MGCorbin/biologically-inspired-perching-drone/images/image(3).png

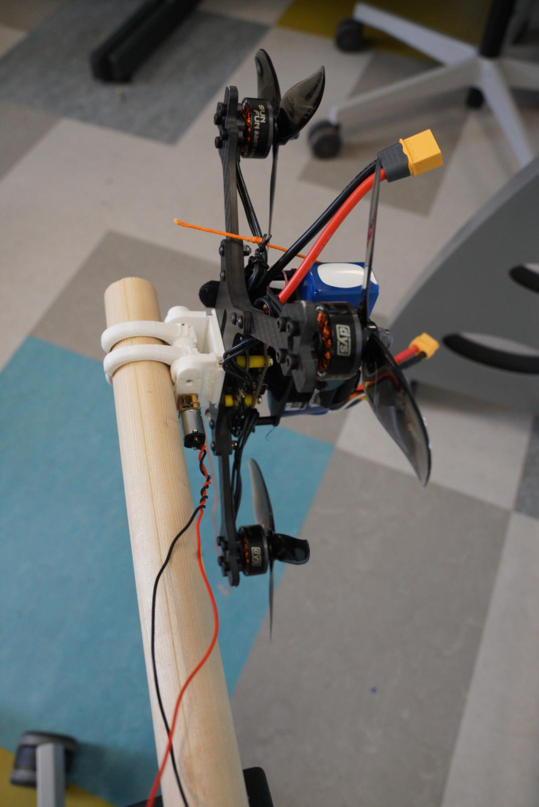
images/image(3).png
