MGCorbin/biologically-inspired-perching-drone/images/image(4).png

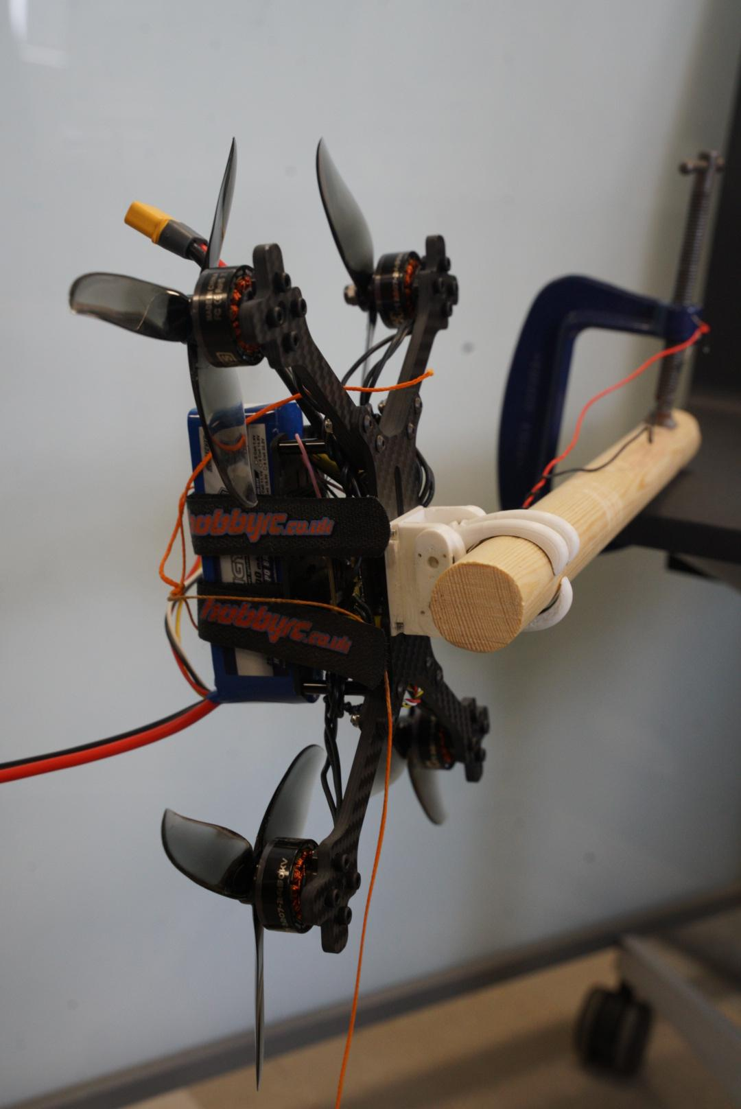
images/image(4).png
