MGCorbin/biologically-inspired-perching-drone/images/image(5).png

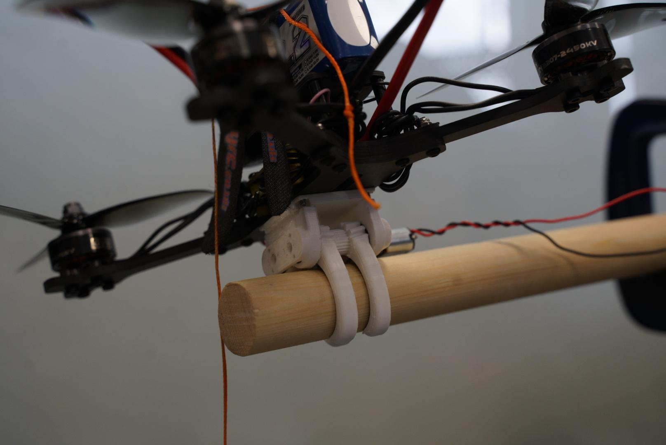
images/image(5).png
