MGCorbin/biologically-inspired-perching-drone/images/image(7).png

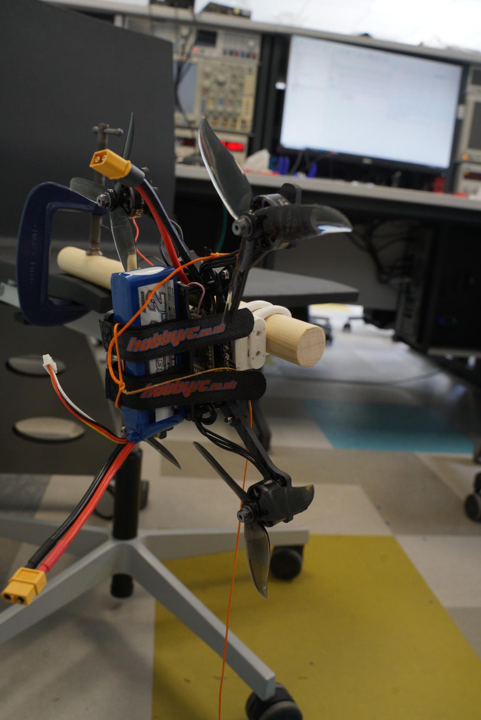
images/image(7).png
