MGCorbin/biologically-inspired-perching-drone/images/image(8).png

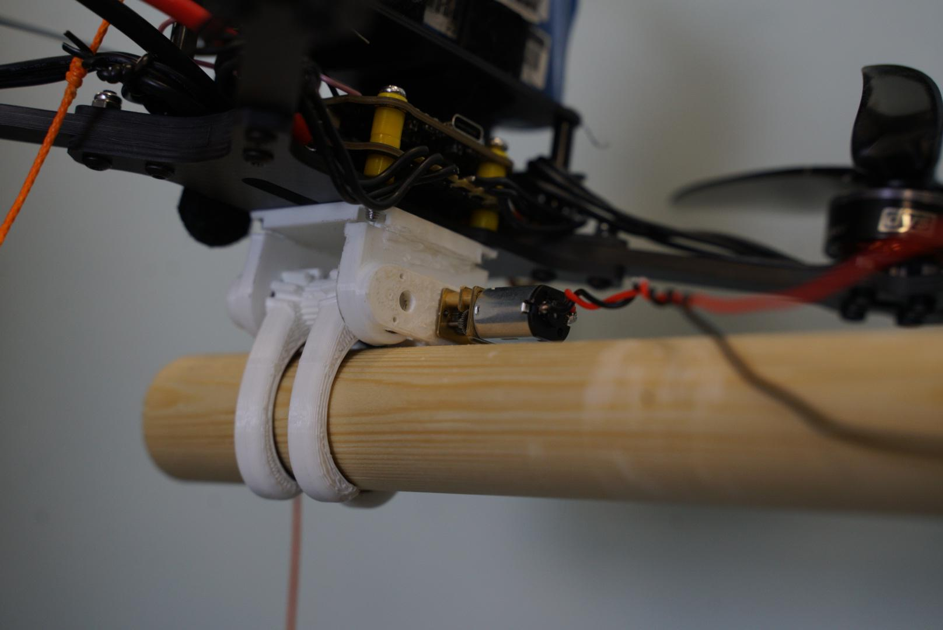
images/image(8).png
