MGCorbin/biologically-inspired-perching-drone/images/image(9).png

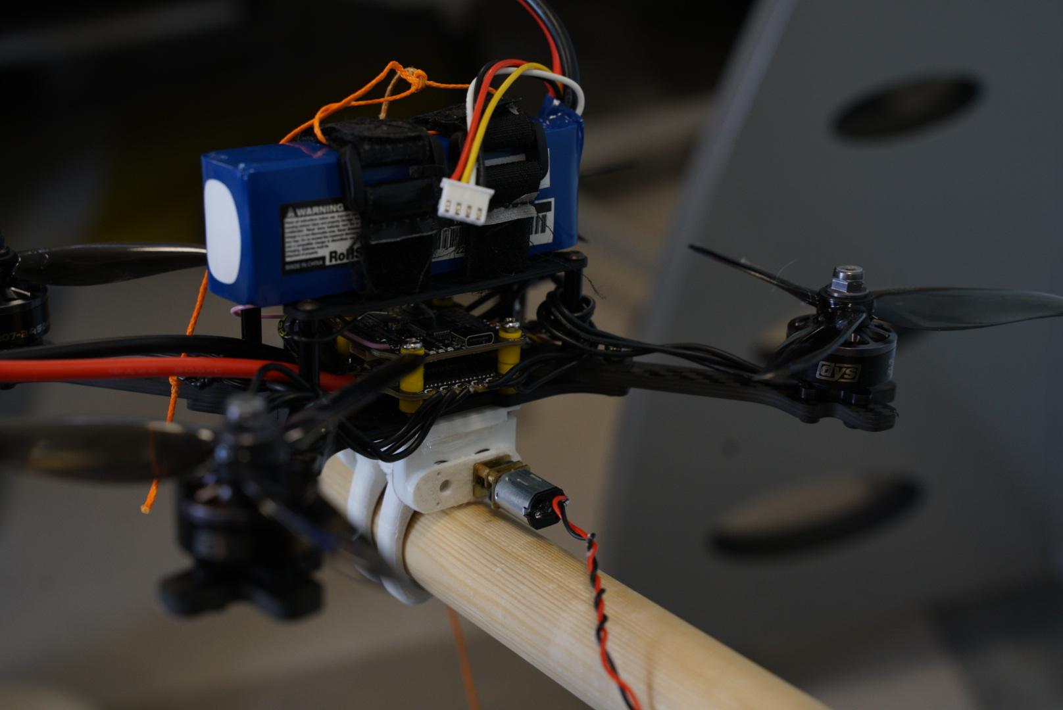
images/image(9).png
