MGCorbin/biologically-inspired-perching-drone/images/image(10).png

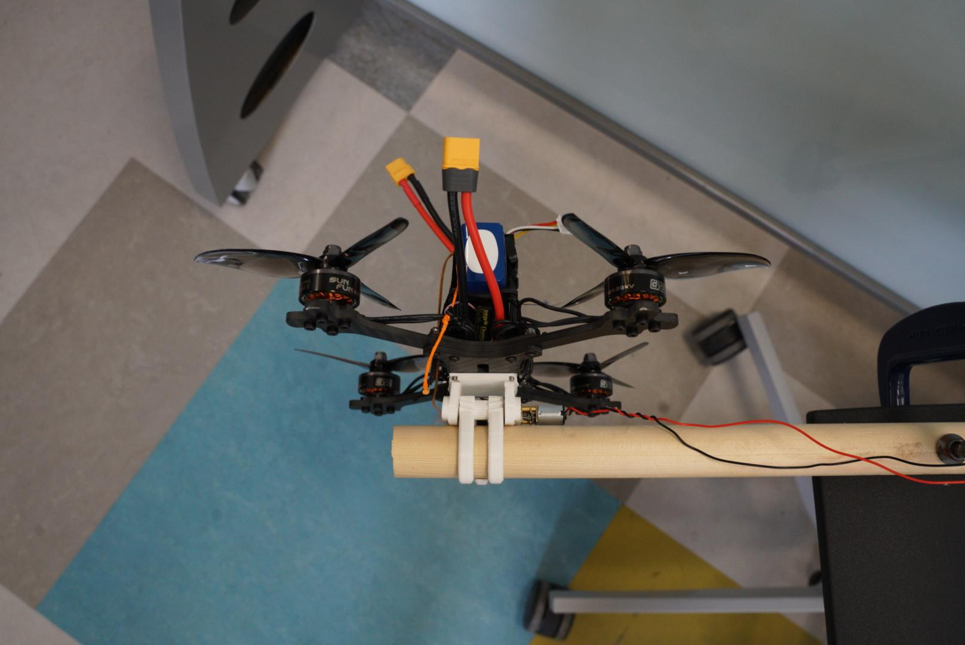
images/image(10).png
