MGCorbin/biologically-inspired-perching-drone/images/image(11).png

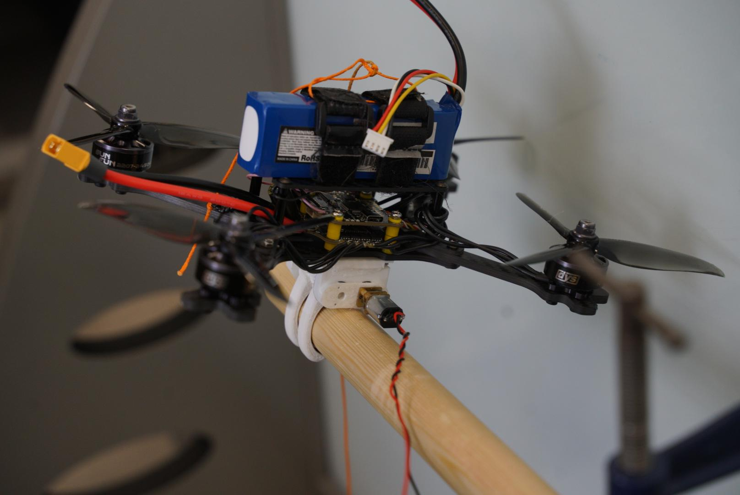
images/image(11).png
