MGCorbin/biologically-inspired-perching-drone/images/image(12).png

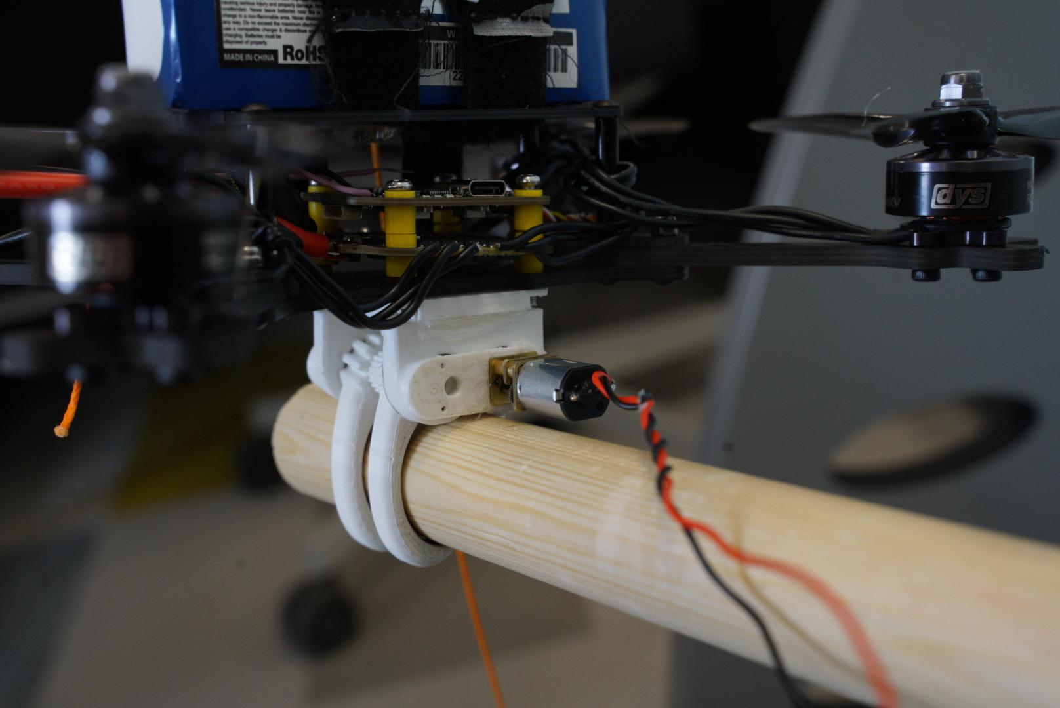
images/image(12).png
