MGCorbin/biologically-inspired-perching-drone/hardware/Large_Scale_Claw/Version3/Assembly1_3_arm_2.stl

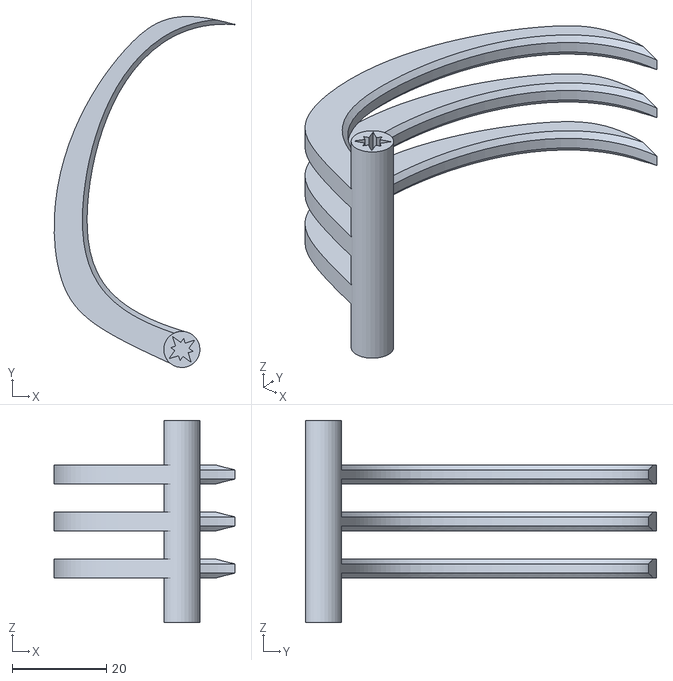
[picture p25: CAD file, 2023-05-17]
hardware/Large_Scale_Claw/Version3/Assembly1_3_arm_2.stl
38.4 x 74.6 x 43.0
