MGCorbin/biologically-inspired-perching-drone/hardware/Bivalve_7_talon/Assem1.SLDASM

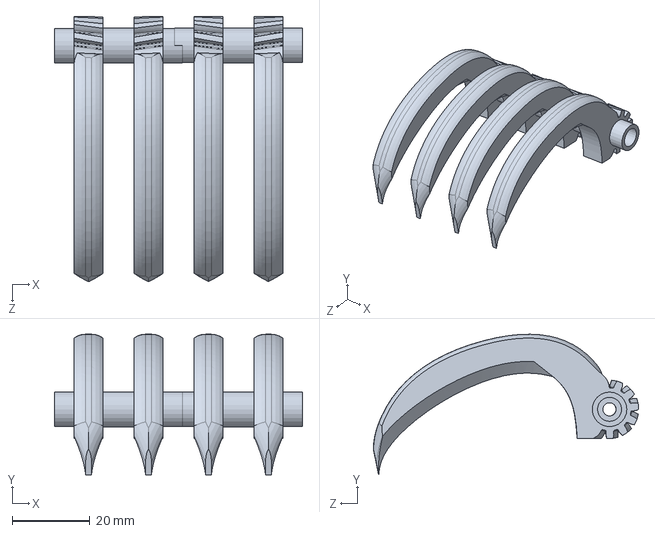
[picture p26: CAD file, 2023-05-12]
hardware/Bivalve_7_talon/Assem1.SLDASM
63.7 x 36.1 x 68.2 mm
Anterior2.new3 x 2
