MGCorbin/biologically-inspired-perching-drone/hardware/Large_Scale_Claw/Version3/Assembly1_base_1.stl

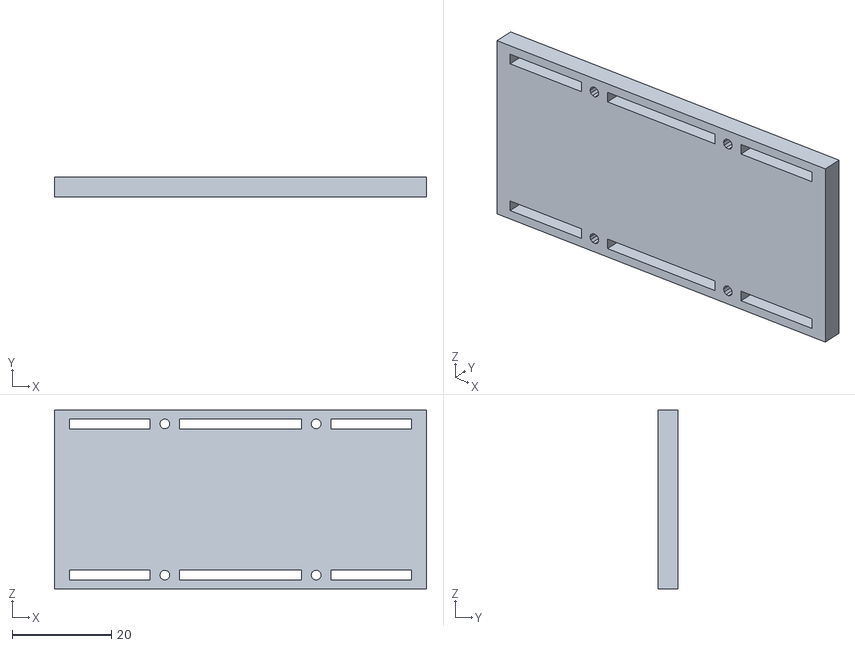
[picture p27: CAD file, 2023-05-17]
hardware/Large_Scale_Claw/Version3/Assembly1_base_1.stl
75.0 x 4.00 x 36.0
