MGCorbin/biologically-inspired-perching-drone/hardware/Bivalve_7_talon/talons4.SLDASM

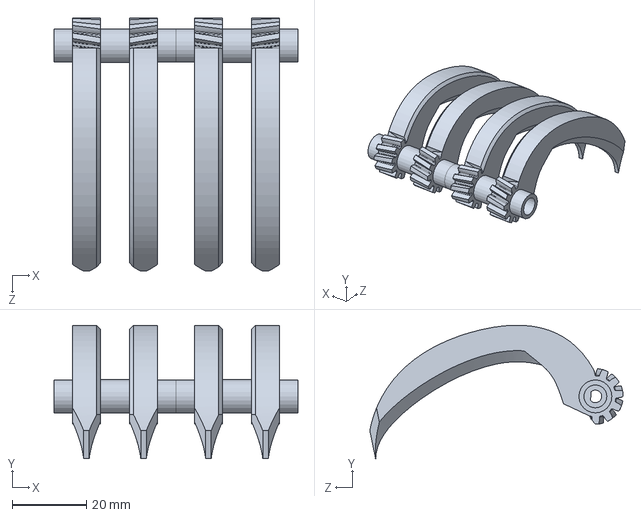
[picture p28: CAD file, 2023-05-12]
hardware/Bivalve_7_talon/talons4.SLDASM
65.8 x 36.0 x 68.3 mm
Anterior2.talons x 2
