MGCorbin/biologically-inspired-perching-drone/hardware/Bivalve_7_talon/Shaftnew.SLDASM

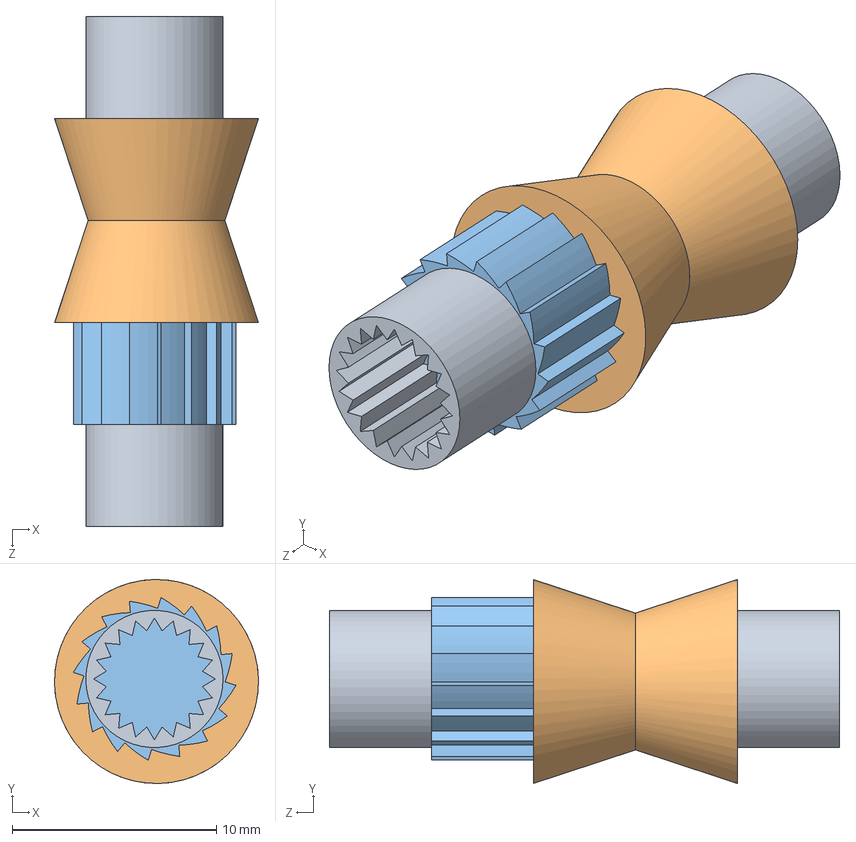
[picture p29: CAD file, 2023-05-12]
hardware/Bivalve_7_talon/Shaftnew.SLDASM
10.0 x 10.0 x 25.0 mm
ServoShaftKey x 2
5m guide new x 2
Gearnew
