MGCorbin/biologically-inspired-perching-drone/hardware/Bivalve_Claw_Mechanism/TopMount.SLDPRT

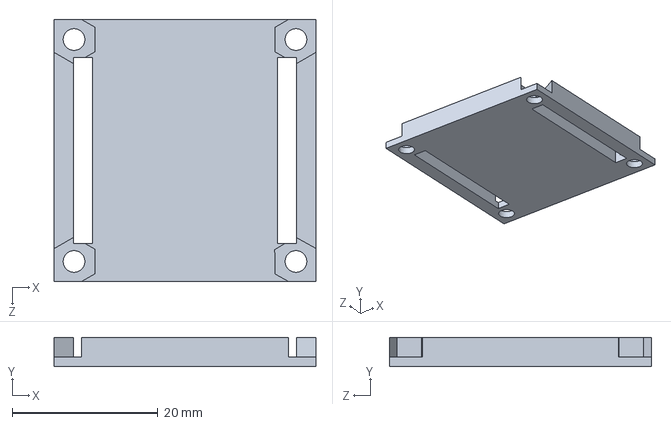
[picture p30: CAD file, 2023-05-12]
hardware/Bivalve_Claw_Mechanism/TopMount.SLDPRT
36.0 x 4.00 x 36.0 mm
