MGCorbin/biologically-inspired-perching-drone/hardware/Large_Scale_Claw/Version3/base.stl

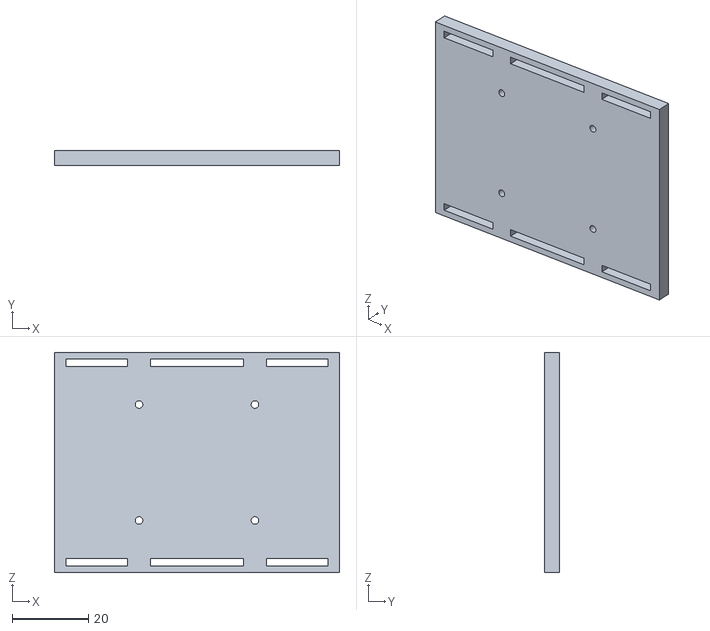
[picture p31: CAD file, 2023-05-19]
hardware/Large_Scale_Claw/Version3/base.stl
75.0 x 4.00 x 58.0
