MGCorbin/biologically-inspired-perching-drone/hardware/Bivalve_7_talon/ServoShaftKey.SLDPRT

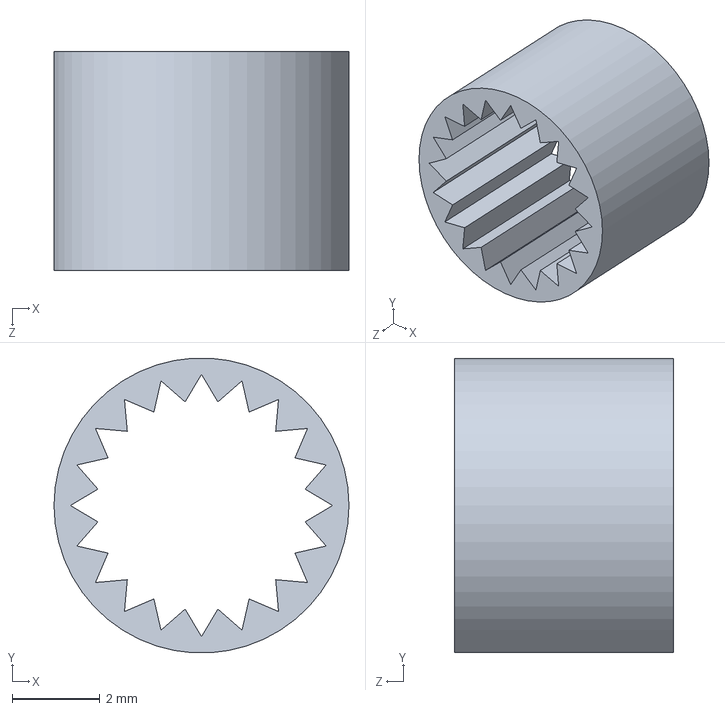
[picture p32: CAD file, 2023-05-12]
hardware/Bivalve_7_talon/ServoShaftKey.SLDPRT
6.72 x 6.71 x 5.00 mm
