MGCorbin/biologically-inspired-perching-drone/hardware/Bivalve_Claw_Mechanism/SideMount12VDC.SLDPRT

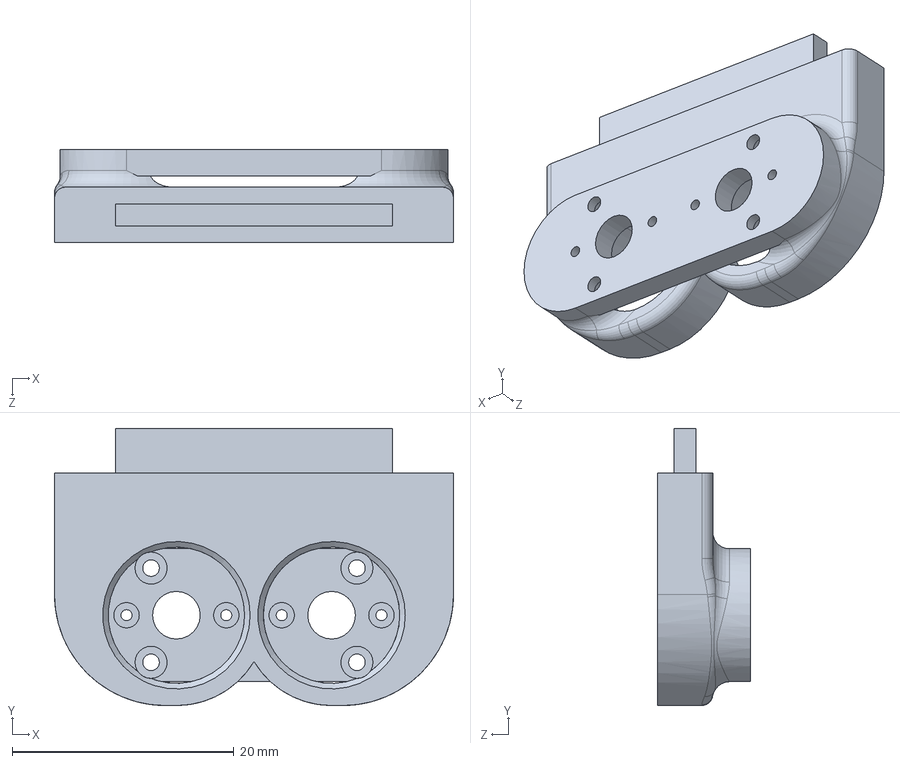
[picture p33: CAD file, 2023-05-12]
hardware/Bivalve_Claw_Mechanism/SideMount12VDC.SLDPRT
36.0 x 25.0 x 8.40 mm
