MGCorbin/biologically-inspired-perching-drone/hardware/Large_Scale_Claw/Version3/3_arm_with_gear.stl

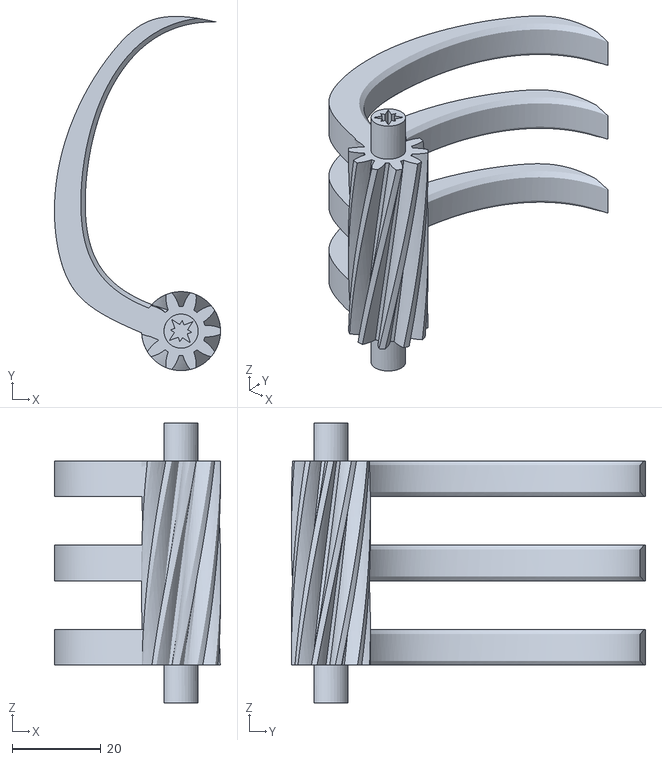
[picture p34: CAD file, 2023-05-19]
hardware/Large_Scale_Claw/Version3/3_arm_with_gear.stl
37.4 x 79.7 x 63.0
