MGCorbin/biologically-inspired-perching-drone/hardware/Bivalve_7_talon/Anterior2.2.SLDPRT

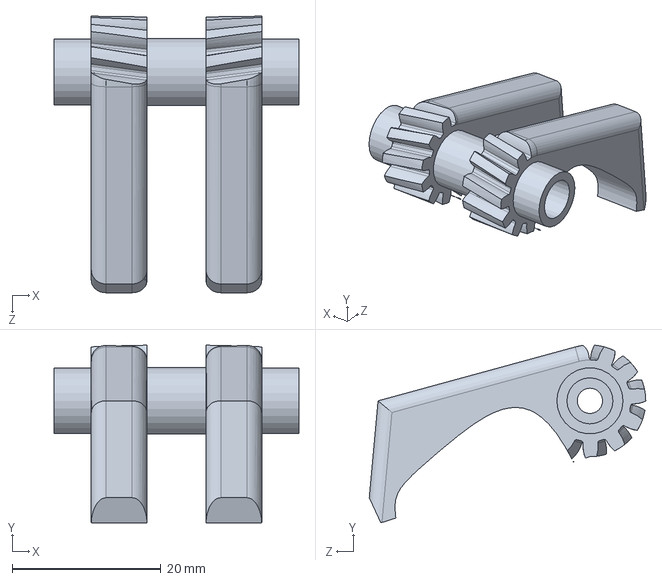
[picture p35: CAD file, 2023-05-12]
hardware/Bivalve_7_talon/Anterior2.2.SLDPRT
32.9 x 23.9 x 37.1 mm
