MGCorbin/biologically-inspired-perching-drone/hardware/Large_Scale_Claw/Version3/2_arm_with_gear.stl

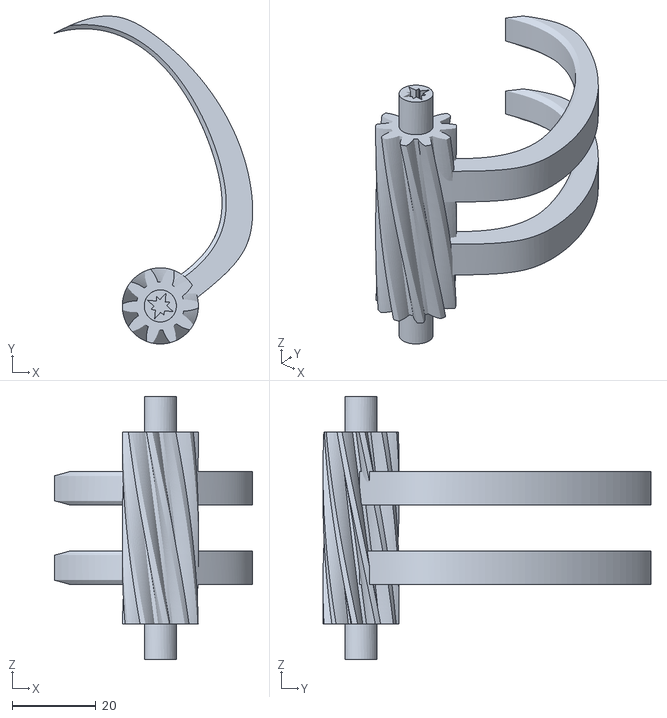
[picture p36: CAD file, 2023-05-19]
hardware/Large_Scale_Claw/Version3/2_arm_with_gear.stl
47.4 x 78.5 x 63.0
