MGCorbin/biologically-inspired-perching-drone/hardware/Tendon_Arm/tendon_segment (1).stl

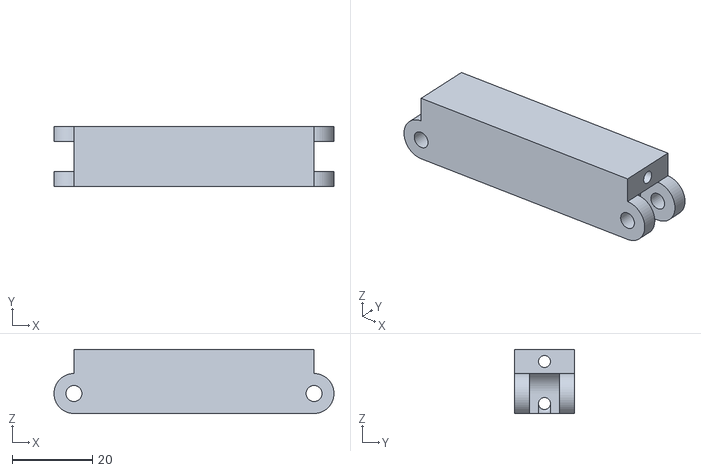
[picture p37: CAD file, 2023-05-12]
hardware/Tendon_Arm/tendon_segment (1).stl
70.0 x 15.0 x 16.0
