MGCorbin/biologically-inspired-perching-drone/hardware/Bivalve_7_talon/3 talon.STL

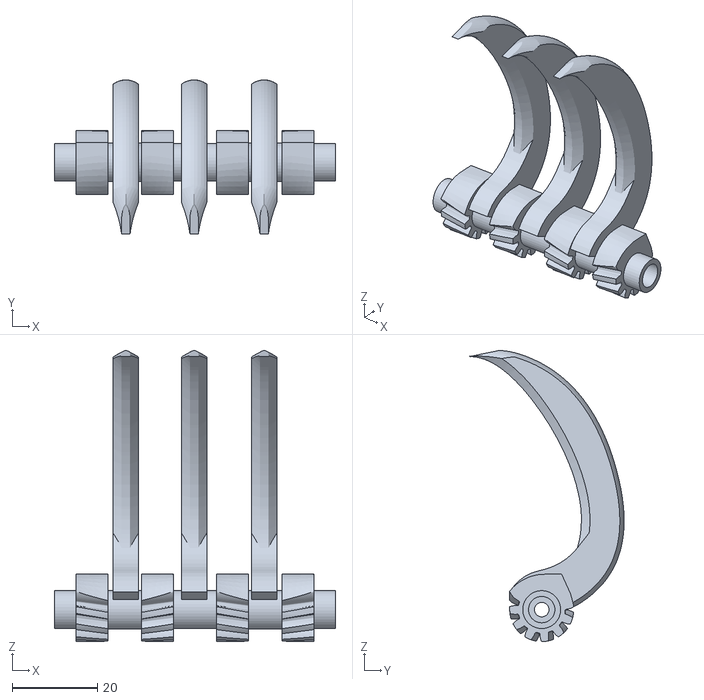
[picture p38: CAD file, 2023-05-12]
hardware/Bivalve_7_talon/3 talon.STL
65.8 x 36.1 x 68.2
