MGCorbin/biologically-inspired-perching-drone/hardware/Bivalve_Claw_Mechanism/PosteriorSingle2.2.SLDPRT

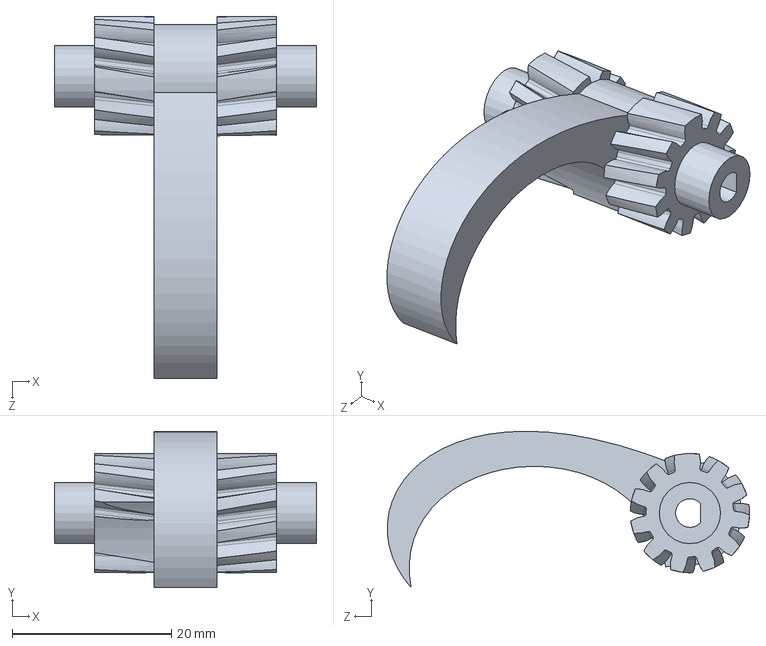
[picture p39: CAD file, 2023-05-12]
hardware/Bivalve_Claw_Mechanism/PosteriorSingle2.2.SLDPRT
32.9 x 19.7 x 45.5 mm
