MGCorbin/biologically-inspired-perching-drone/hardware/Large_Scale_Claw/Version3/wall_2.stl

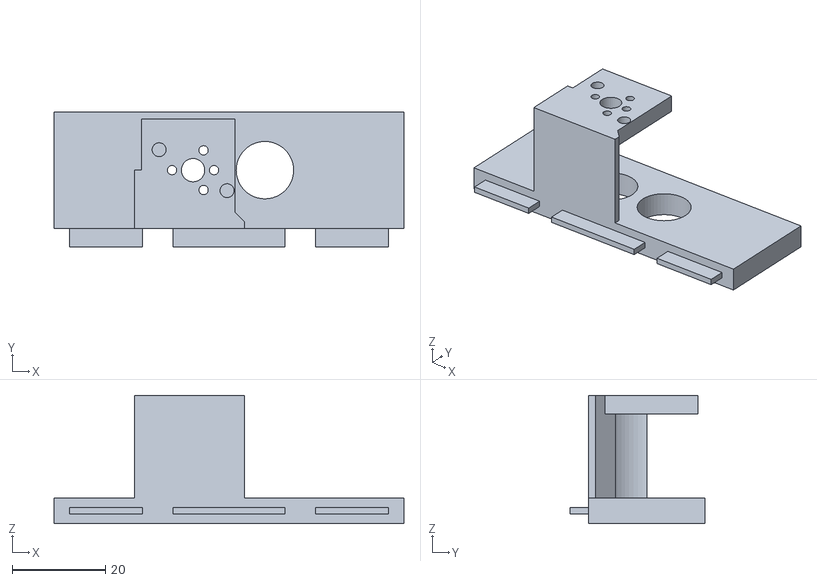
[picture p40: CAD file, 2023-05-19]
hardware/Large_Scale_Claw/Version3/wall_2.stl
75.0 x 29.0 x 27.5
