MGCorbin/biologically-inspired-perching-drone/hardware/Bivalve_7_talon/4 talon2.STL

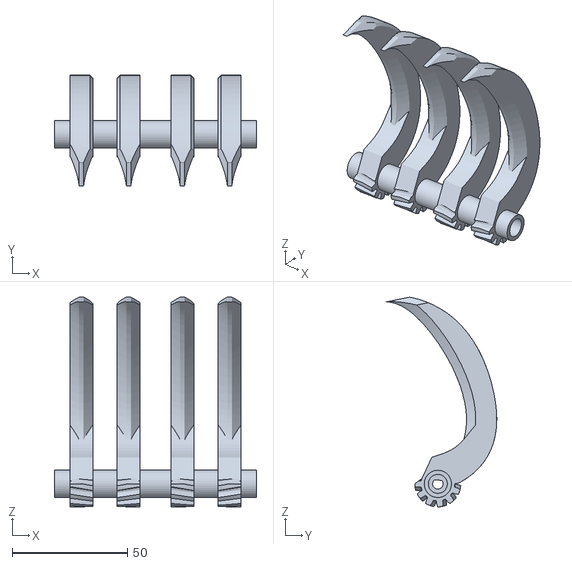
[picture p41: CAD file, 2023-05-12]
hardware/Bivalve_7_talon/4 talon2.STL
87.7 x 48.0 x 91.1
