MGCorbin/biologically-inspired-perching-drone/hardware/Tendon_Arm/tendon_segment2 (2).stl

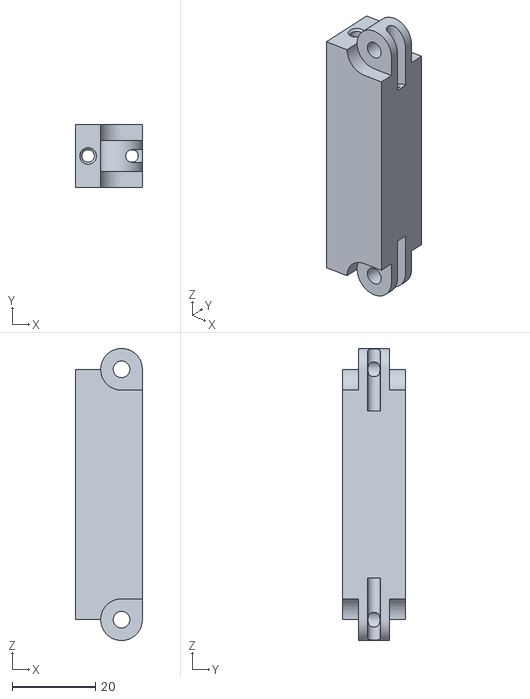
[picture p42: CAD file, 2023-05-12]
hardware/Tendon_Arm/tendon_segment2 (2).stl
16.0 x 15.0 x 70.0
