MGCorbin/biologically-inspired-perching-drone/hardware/Bivalve_7_talon/4 talonscaled.SLDPRT

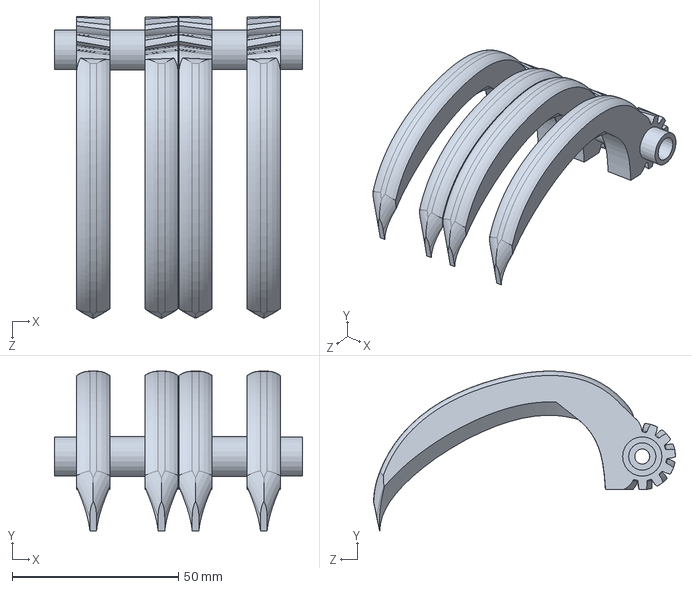
[picture p43: CAD file, 2023-05-12]
hardware/Bivalve_7_talon/4 talonscaled.SLDPRT
74.7 x 48.1 x 90.9 mm
