MGCorbin/biologically-inspired-perching-drone/hardware/Bivalve_Claw_Mechanism/Anterior2.2.SLDPRT

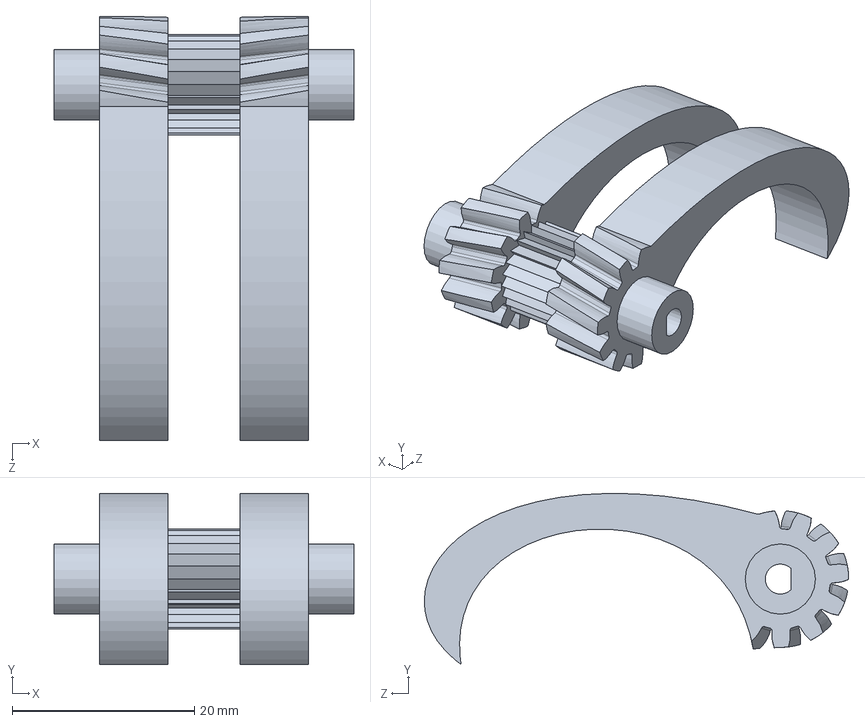
[picture p44: CAD file, 2023-05-12]
hardware/Bivalve_Claw_Mechanism/Anterior2.2.SLDPRT
32.9 x 18.8 x 46.5 mm
