MGCorbin/biologically-inspired-perching-drone/hardware/Tendon_Arm/double_base.stl

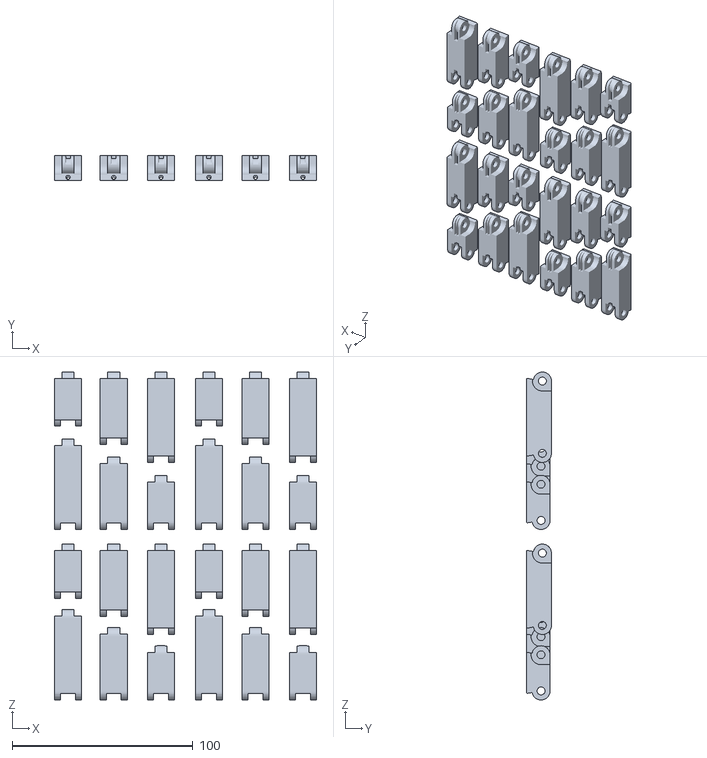
[picture p45: CAD file, 2023-05-12]
hardware/Tendon_Arm/double_base.stl
144.9 x 13.8 x 181.3
