MGCorbin/biologically-inspired-perching-drone/hardware/Bivalve_7_talon/5m guide new.SLDPRT

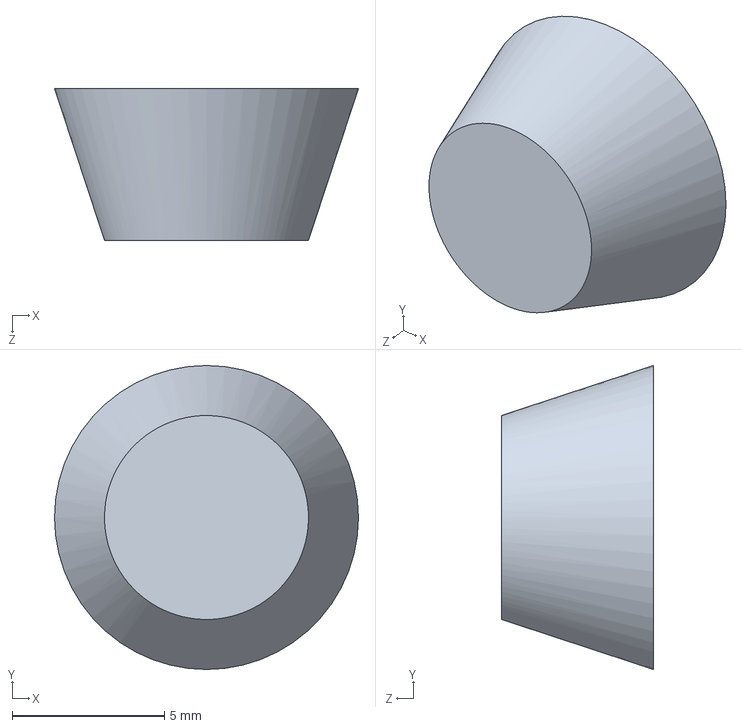
[picture p46: CAD file, 2023-05-12]
hardware/Bivalve_7_talon/5m guide new.SLDPRT
10.0 x 10.0 x 5.00 mm
