MGCorbin/biologically-inspired-perching-drone/hardware/Bivalve_7_talon/Anterior2.talons.SLDPRT

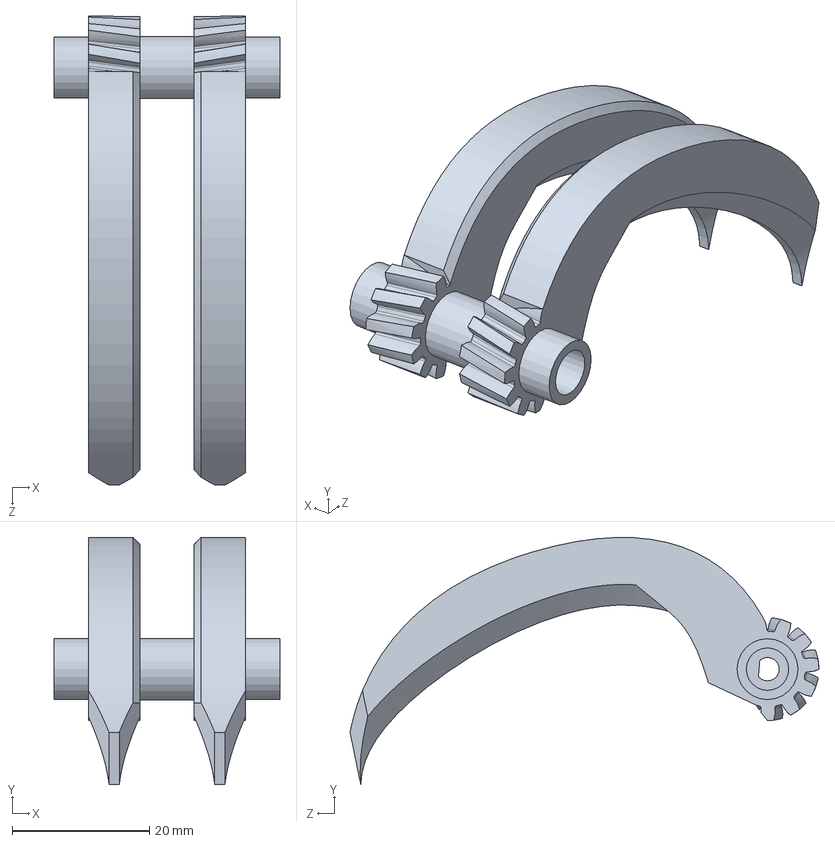
[picture p47: CAD file, 2023-05-12]
hardware/Bivalve_7_talon/Anterior2.talons.SLDPRT
32.9 x 36.0 x 68.3 mm
