MGCorbin/biologically-inspired-perching-drone/hardware/Tendon_Arm/tendon_C2.stl

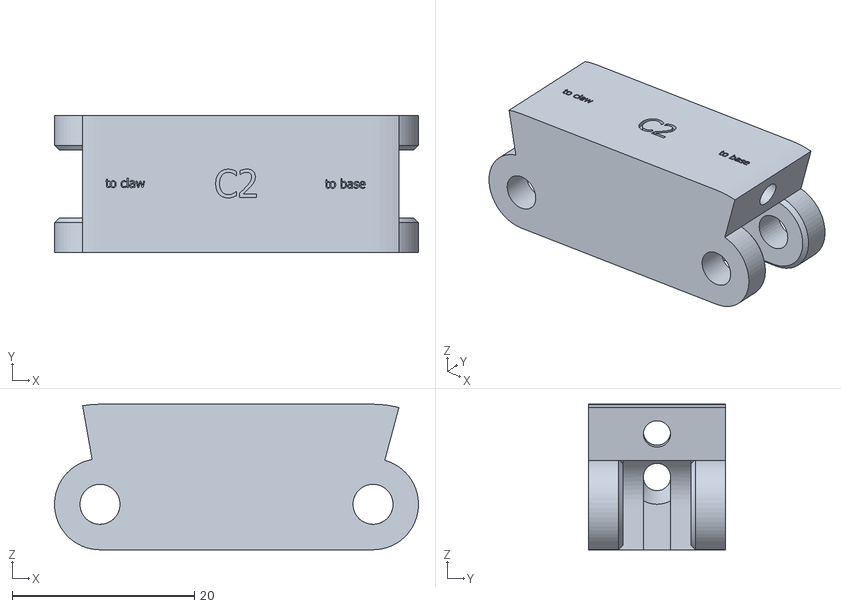
[picture p48: CAD file, 2023-05-12]
hardware/Tendon_Arm/tendon_C2.stl
40.0 x 15.0 x 16.0
