MGCorbin/biologically-inspired-perching-drone/hardware/Bivalve_7_talon/Anterior2.new3scaled.SLDPRT

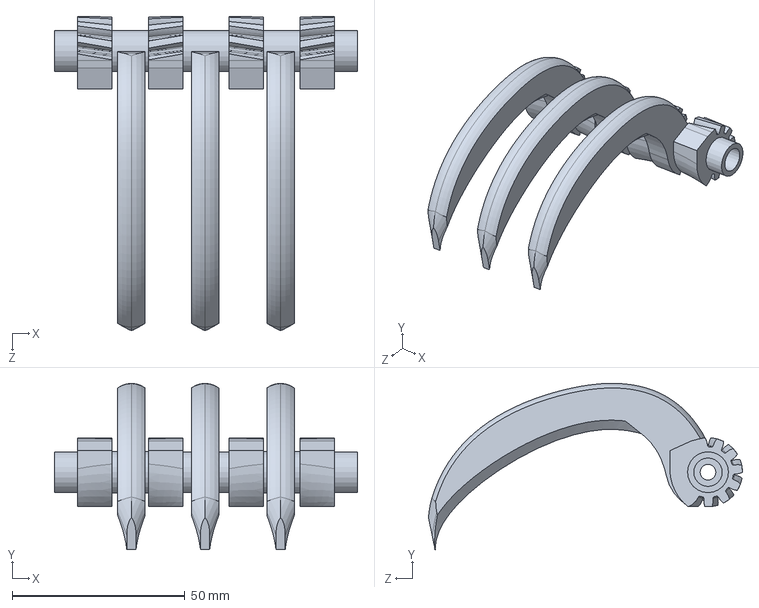
[picture p49: CAD file, 2023-05-12]
hardware/Bivalve_7_talon/Anterior2.new3scaled.SLDPRT
87.7 x 48.1 x 90.9 mm
