MGCorbin/biologically-inspired-perching-drone/hardware/Bivalve_7_talon/Gearnew.SLDPRT

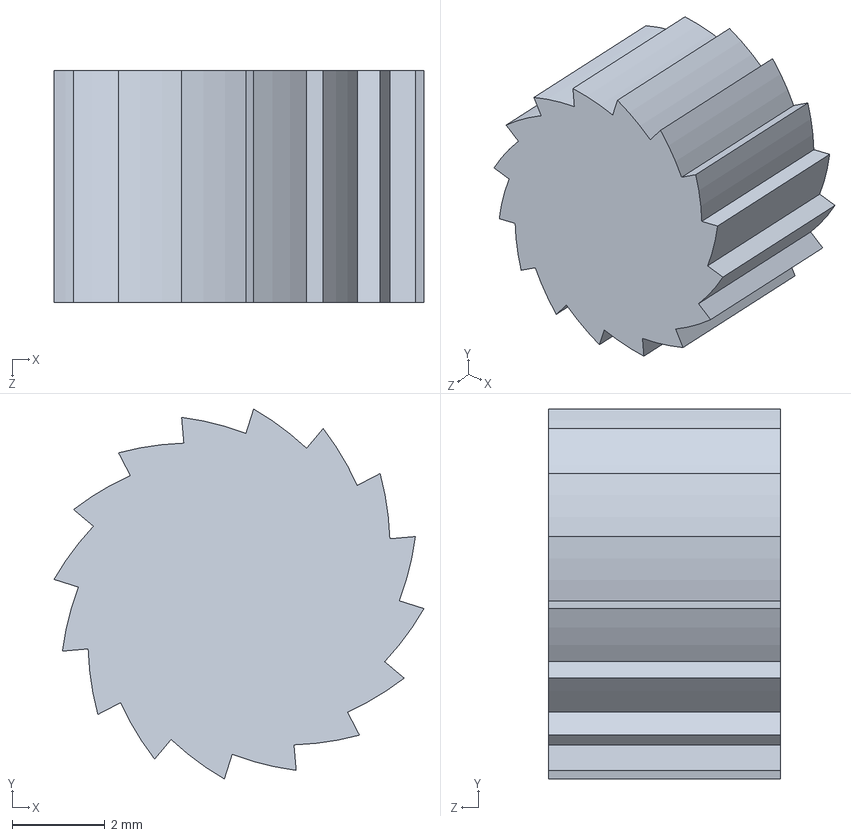
[picture p50: CAD file, 2023-05-12]
hardware/Bivalve_7_talon/Gearnew.SLDPRT
7.98 x 7.98 x 5.00 mm
