MGCorbin/biologically-inspired-perching-drone/hardware/Bivalve_7_talon/Basenew.SLDPRT

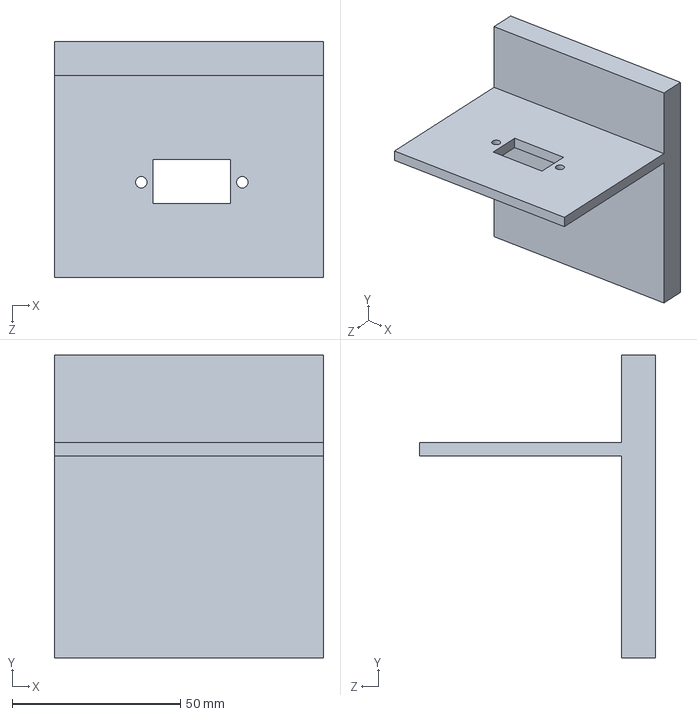
[picture p51: CAD file, 2023-05-12]
hardware/Bivalve_7_talon/Basenew.SLDPRT
80.0 x 90.0 x 70.0 mm
